jaromir-sukuba/nvm/media/enc_2.jpg

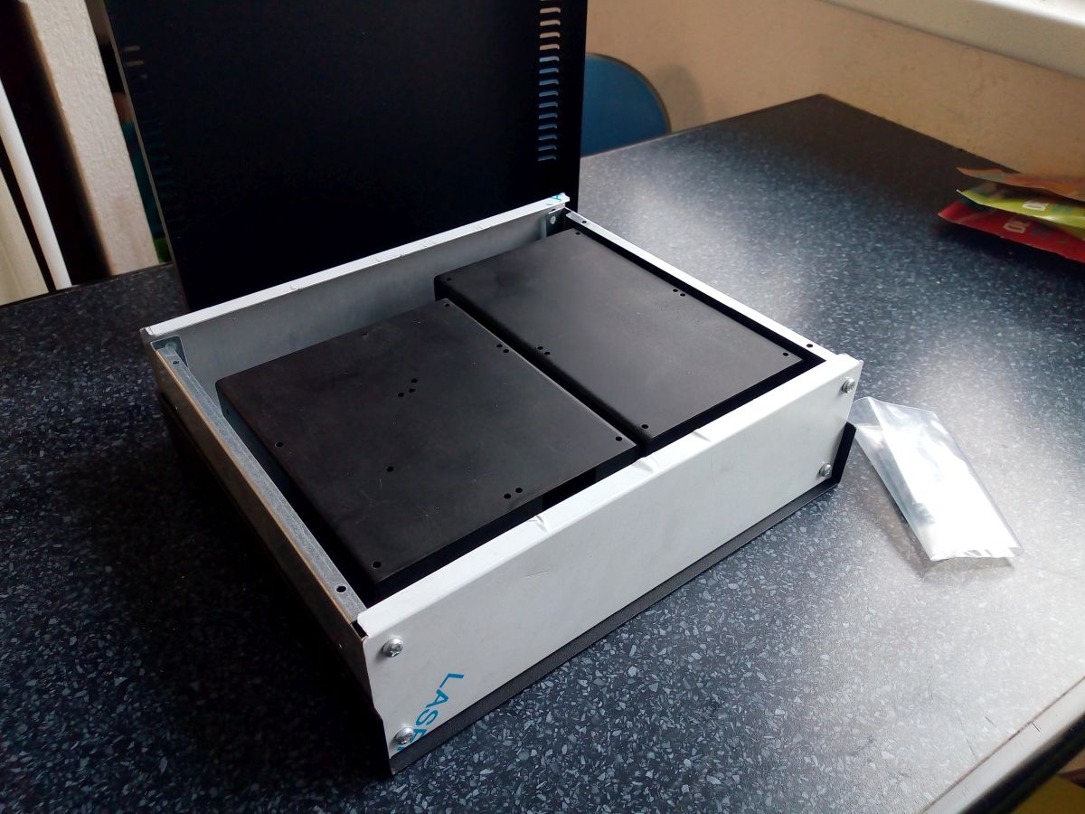
media/enc_2.jpg
