jaromir-sukuba/nvm/media/IMG_0008_.jpg

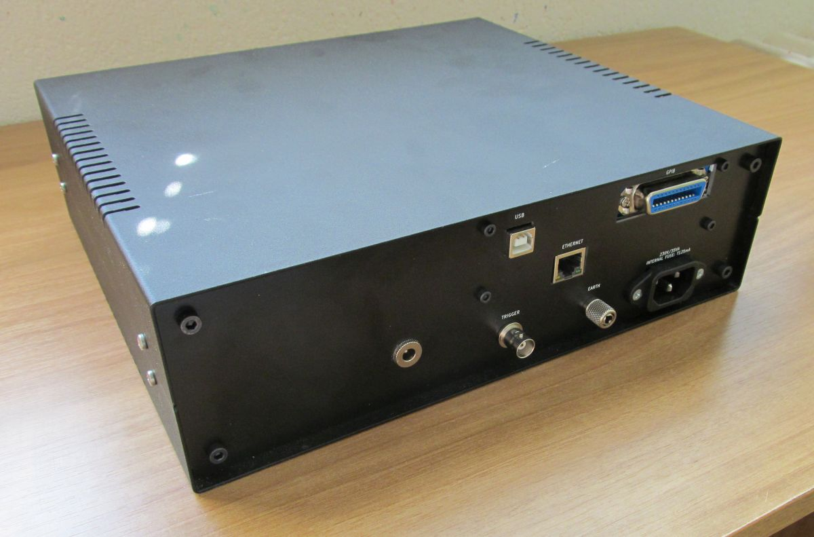
media/IMG_0008_.jpg
