jaromir-sukuba/nvm/media/IMG_0013_.jpg

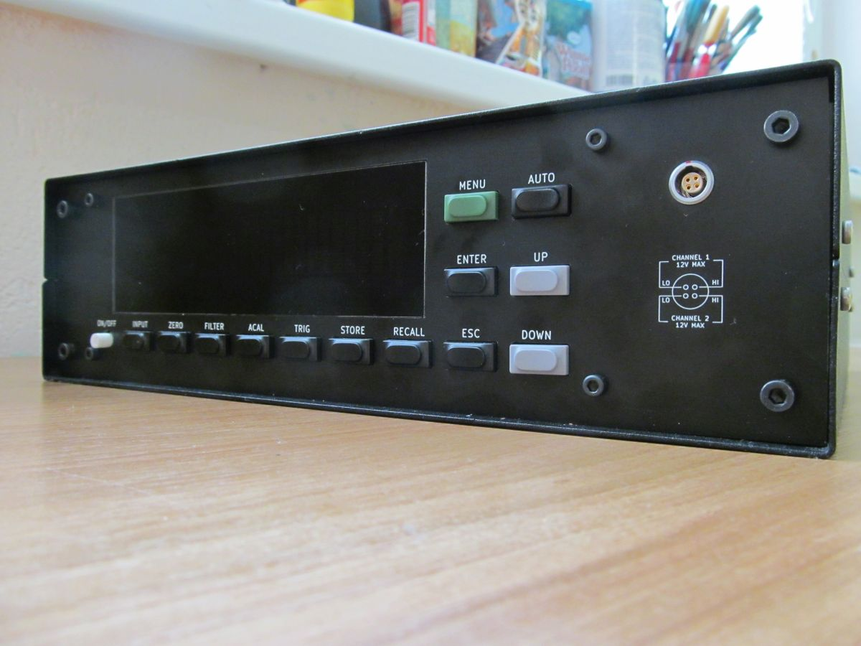
media/IMG_0013_.jpg
