jaromir-sukuba/nvm/media/IMG_0014_.jpg

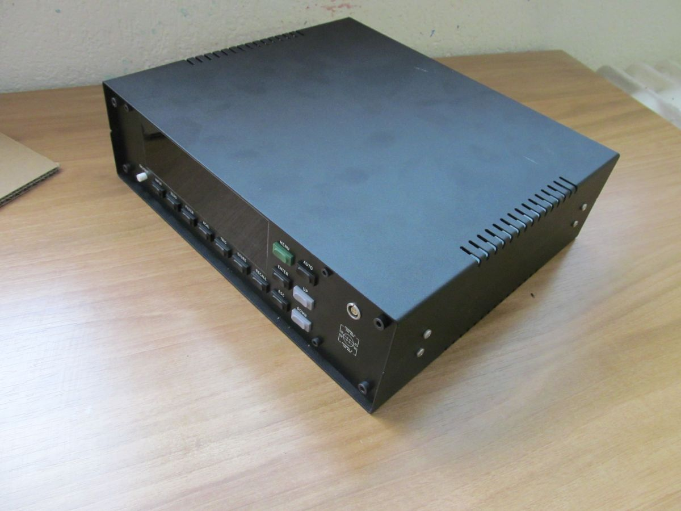
media/IMG_0014_.jpg
