jaromir-sukuba/nvm/firmware/STM32/nvm_373_2/Inc/acal.h

/*
 * acal.h
 *
 *  Created on: May 12, 2022
 *      Author: jarin
 */

#ifndef ACAL_H_
#define ACAL_H_

void main_state_acal (void);
#define		ACAL_CYC_WAIT		1
#define		ACAL_CYC_AVERAGE	3
#define		ACAL_NPLC_SET		7
#define		ACAL_STEPS			14


#endif /* ACAL_H_ */
